ahmadtak-3212/flashlight_project/electrical/flashlight-full-v1-1/docs/Images/usbc.jpeg

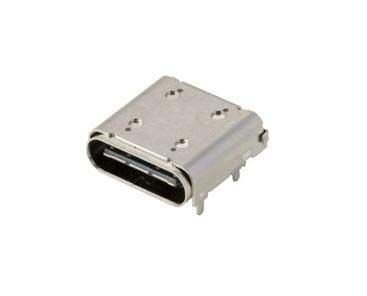
electrical/flashlight-full-v1-1/docs/Images/usbc.jpeg
