ahmadtak-3212/flashlight_project/firmware/flashlight-firmware-stm32/boards/platforms/ststm32/examples/mbed-rtos-custom-target/src/TARGET_STM32L452xE/TARGET_NUCLEO_L452RE_P/PeripheralPins.c

/* mbed Microcontroller Library
 *******************************************************************************
 * Copyright (c) 2019, STMicroelectronics
 * All rights reserved.
 *
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
 * Automatically generated from STM32L452RETxP.xml
 */

#include "PeripheralPins.h"
#include "mbed_toolchain.h"

//==============================================================================
// Notes
//
// - The pins mentioned Px_y_ALTz are alternative possibilities which use other
//   HW peripheral instances. You can use them the same way as any other "normal"
//   pin (i.e. PwmOut pwm(PA_7_ALT0);). These pins are not displayed on the board
//   pinout image on mbed.org.
//
// - The pins which are connected to other components present on the board have
//   the comment "Connected to xxx". The pin function may not work properly in this
//   case. These pins may not be displayed on the board pinout image on mbed.org.
//   Please read the board reference manual and schematic for more information.
//
// - Warning: pins connected to the default STDIO_UART_TX and STDIO_UART_RX pins are commented
//   See https://os.mbed.com/teams/ST/wiki/STDIO for more information.
//
//==============================================================================


//*** ADC ***

MBED_WEAK const PinMap PinMap_ADC[] = {
    {PA_0,       ADC_1, STM_PIN_DATA_EXT(STM_MODE_ANALOG, GPIO_NOPULL, 0, 5, 0)}, // ADC1_IN5
    {PA_1,       ADC_1, STM_PIN_DATA_EXT(STM_MODE_ANALOG, GPIO_NOPULL, 0, 6, 0)}, // ADC1_IN6
//  {PA_2,       ADC_1, STM_PIN_DATA_EXT(STM_MODE_ANALOG, GPIO_NOPULL, 0, 7, 0)}, // ADC1_IN7 // Connected to STDIO_UART_TX
//  {PA_3,       ADC_1, STM_PIN_DATA_EXT(STM_MODE_ANALOG, GPIO_NOPULL, 0, 8, 0)}, // ADC1_IN8 // Connected to STDIO_UART_RX
    {PA_4,       ADC_1, STM_PIN_DATA_EXT(STM_MODE_ANALOG, GPIO_NOPULL, 0, 9, 0)}, // ADC1_IN9 // Connected to SMPS_EN [ADP5301ACBZ_VEN]
    {PA_5,       ADC_1, STM_PIN_DATA_EXT(STM_MODE_ANALOG, GPIO_NOPULL, 0, 10, 0)}, // ADC1_IN10 // Connected to SMPS_V1
    {PA_6,       ADC_1, STM_PIN_DATA_EXT(STM_MODE_ANALOG, GPIO_NOPULL, 0, 11, 0)}, // ADC1_IN11 // Connected to SMPS_PG [ADP5301ACBZ_OUTOK]
    {PA_7,       ADC_1, STM_PIN_DATA_EXT(STM_MODE_ANALOG, GPIO_NOPULL, 0, 12, 0)}, // ADC1_IN12 // Connected to SMPS_SW [TS3A44159PWR_IN1_2]
    {PB_0,       ADC_1, STM_PIN_DATA_EXT(STM_MODE_ANALOG, GPIO_NOPULL, 0, 15, 0)}, // ADC1_IN15
    {PB_1,       ADC_1, STM_PIN_DATA_EXT(STM_MODE_ANALOG, GPIO_NOPULL, 0, 16, 0)}, // ADC1_IN16
    {PC_0,       ADC_1, STM_PIN_DATA_EXT(STM_MODE_ANALOG, GPIO_NOPULL, 0, 1, 0)}, // ADC1_IN1
    {PC_1,       ADC_1, STM_PIN_DATA_EXT(STM_MODE_ANALOG, GPIO_NOPULL, 0, 2, 0)}, // ADC1_IN2
    {PC_2,       ADC_1, STM_PIN_DATA_EXT(STM_MODE_ANALOG, GPIO_NOPULL, 0, 3, 0)}, // ADC1_IN3
    {PC_3,       ADC_1, STM_PIN_DATA_EXT(STM_MODE_ANALOG, GPIO_NOPULL, 0, 4, 0)}, // ADC1_IN4
    {PC_4,       ADC_1, STM_PIN_DATA_EXT(STM_MODE_ANALOG, GPIO_NOPULL, 0, 13, 0)}, // ADC1_IN13
    {NC, NC, 0}
};

// !!! SECTION TO BE CHECKED WITH DEVICE REFERENCE MANUAL
MBED_WEAK const PinMap PinMap_ADC_Internal[] = {
    {ADC_TEMP,   ADC_1,    STM_PIN_DATA_EXT(STM_MODE_ANALOG, GPIO_NOPULL, 0, 16, 0)},
    {ADC_VREF,   ADC_1,    STM_PIN_DATA_EXT(STM_MODE_ANALOG, GPIO_NOPULL, 0, 17, 0)},
    {ADC_VBAT,   ADC_1,    STM_PIN_DATA_EXT(STM_MODE_ANALOG, GPIO_NOPULL, 0, 18, 0)},
    {NC, NC, 0}
};

//*** DAC ***

MBED_WEAK const PinMap PinMap_DAC[] = {
    {PA_4,       DAC_1, STM_PIN_DATA_EXT(STM_MODE_ANALOG, GPIO_NOPULL, 0, 1, 0)}, // DAC1_OUT1 // Connected to SMPS_EN [ADP5301ACBZ_VEN]
    {NC, NC, 0}
};

//*** I2C ***

MBED_WEAK const PinMap PinMap_I2C_SDA[] = {
    {PA_10,      I2C_1, STM_PIN_DATA(STM_MODE_AF_OD, GPIO_NOPULL, GPIO_AF4_I2C1)},
    {PB_4,       I2C_3, STM_PIN_DATA(STM_MODE_AF_OD, GPIO_NOPULL, GPIO_AF4_I2C3)},
    {PB_7,       I2C_1, STM_PIN_DATA(STM_MODE_AF_OD, GPIO_NOPULL, GPIO_AF4_I2C1)},
    {PB_7_ALT0,  I2C_4, STM_PIN_DATA(STM_MODE_AF_OD, GPIO_NOPULL, GPIO_AF5_I2C4)},
    {PB_9,       I2C_1, STM_PIN_DATA(STM_MODE_AF_OD, GPIO_NOPULL, GPIO_AF4_I2C1)},
    {PB_11,      I2C_2, STM_PIN_DATA(STM_MODE_AF_OD, GPIO_NOPULL, GPIO_AF4_I2C2)},
    {PB_11_ALT0, I2C_4, STM_PIN_DATA(STM_MODE_AF_OD, GPIO_NOPULL, GPIO_AF3_I2C4)},
    {PB_14,      I2C_2, STM_PIN_DATA(STM_MODE_AF_OD, GPIO_NOPULL, GPIO_AF4_I2C2)},
    {PC_1,       I2C_3, STM_PIN_DATA(STM_MODE_AF_OD, GPIO_NOPULL, GPIO_AF4_I2C3)},
    {PC_1_ALT0,  I2C_4, STM_PIN_DATA(STM_MODE_AF_OD, GPIO_NOPULL, GPIO_AF2_I2C4)},
    {NC, NC, 0}
};

MBED_WEAK const PinMap PinMap_I2C_SCL[] = {
    {PA_7,       I2C_3, STM_PIN_DATA(STM_MODE_AF_OD, GPIO_NOPULL, GPIO_AF4_I2C3)}, // Connected to SMPS_SW [TS3A44159PWR_IN1_2]
    {PA_9,       I2C_1, STM_PIN_DATA(STM_MODE_AF_OD, GPIO_NOPULL, GPIO_AF4_I2C1)},
    {PB_6,       I2C_1, STM_PIN_DATA(STM_MODE_AF_OD, GPIO_NOPULL, GPIO_AF4_I2C1)},
    {PB_6_ALT0,  I2C_4, STM_PIN_DATA(STM_MODE_AF_OD, GPIO_NOPULL, GPIO_AF5_I2C4)},
    {PB_8,       I2C_1, STM_PIN_DATA(STM_MODE_AF_OD, GPIO_NOPULL, GPIO_AF4_I2C1)},
    {PB_10,      I2C_2, STM_PIN_DATA(STM_MODE_AF_OD, GPIO_NOPULL, GPIO_AF4_I2C2)},
    {PB_10_ALT0, I2C_4, STM_PIN_DATA(STM_MODE_AF_OD, GPIO_NOPULL, GPIO_AF3_I2C4)},
    {PB_13,      I2C_2, STM_PIN_DATA(STM_MODE_AF_OD, GPIO_NOPULL, GPIO_AF4_I2C2)}, // Connected to LD4 [green Led]
    {PC_0,       I2C_3, STM_PIN_DATA(STM_MODE_AF_OD, GPIO_NOPULL, GPIO_AF4_I2C3)},
    {PC_0_ALT0,  I2C_4, STM_PIN_DATA(STM_MODE_AF_OD, GPIO_NOPULL, GPIO_AF2_I2C4)},
    {NC, NC, 0}
};

//*** PWM ***

// TIM2 cannot be used because already used by the us_ticker
// You have to comment all PWM using TIM_MST defined in hal_tick.h file
//  or update python script (check TIM_MST_LIST) and re-run it
MBED_WEAK const PinMap PinMap_PWM[] = {
//  {PA_0,       PWM_2,  STM_PIN_DATA_EXT(STM_MODE_AF_PP, GPIO_NOPULL, GPIO_AF1_TIM2, 1, 0)}, // TIM2_CH1 // TIM2 used by us_ticker
//  {PA_1,       PWM_2,  STM_PIN_DATA_EXT(STM_MODE_AF_PP, GPIO_NOPULL, GPIO_AF1_TIM2, 2, 0)}, // TIM2_CH2 // TIM2 used by us_ticker
    {PA_1,       PWM_15, STM_PIN_DATA_EXT(STM_MODE_AF_PP, GPIO_NOPULL, GPIO_AF14_TIM15, 1, 1)}, // TIM15_CH1N
//  {PA_2,       PWM_2,  STM_PIN_DATA_EXT(STM_MODE_AF_PP, GPIO_NOPULL, GPIO_AF1_TIM2, 3, 0)}, // TIM2_CH3 // Connected to STDIO_UART_TX
//  {PA_2,       PWM_15, STM_PIN_DATA_EXT(STM_MODE_AF_PP, GPIO_NOPULL, GPIO_AF14_TIM15, 1, 0)}, // TIM15_CH1 // Connected to STDIO_UART_TX
//  {PA_3,       PWM_2,  STM_PIN_DATA_EXT(STM_MODE_AF_PP, GPIO_NOPULL, GPIO_AF1_TIM2, 4, 0)}, // TIM2_CH4 // Connected to STDIO_UART_RX
//  {PA_3,       PWM_15, STM_PIN_DATA_EXT(STM_MODE_AF_PP, GPIO_NOPULL, GPIO_AF14_TIM15, 2, 0)}, // TIM15_CH2 // Connected to STDIO_UART_RX
//  {PA_5,       PWM_2,  STM_PIN_DATA_EXT(STM_MODE_AF_PP, GPIO_NOPULL, GPIO_AF1_TIM2, 1, 0)}, // TIM2_CH1 // Connected to SMPS_V1, TIM2 used by us_ticker
    {PA_6,       PWM_3,  STM_PIN_DATA_EXT(STM_MODE_AF_PP, GPIO_NOPULL, GPIO_AF2_TIM3, 1, 0)}, // TIM3_CH1 // Connected to SMPS_PG [ADP5301ACBZ_OUTOK]
    {PA_6_ALT0,  PWM_16, STM_PIN_DATA_EXT(STM_MODE_AF_PP, GPIO_NOPULL, GPIO_AF14_TIM16, 1, 0)}, // TIM16_CH1 // Connected to SMPS_PG [ADP5301ACBZ_OUTOK]
    {PA_7,       PWM_1,  STM_PIN_DATA_EXT(STM_MODE_AF_PP, GPIO_NOPULL, GPIO_AF1_TIM1, 1, 1)}, // TIM1_CH1N // Connected to SMPS_SW [TS3A44159PWR_IN1_2]
    {PA_7_ALT0,  PWM_3,  STM_PIN_DATA_EXT(STM_MODE_AF_PP, GPIO_NOPULL, GPIO_AF2_TIM3, 2, 0)}, // TIM3_CH2 // Connected to SMPS_SW [TS3A44159PWR_IN1_2]
    {PA_8,       PWM_1,  STM_PIN_DATA_EXT(STM_MODE_AF_PP, GPIO_NOPULL, GPIO_AF1_TIM1, 1, 0)}, // TIM1_CH1
    {PA_9,       PWM_1,  STM_PIN_DATA_EXT(STM_MODE_AF_PP, GPIO_NOPULL, GPIO_AF1_TIM1, 2, 0)}, // TIM1_CH2
    {PA_10,      PWM_1,  STM_PIN_DATA_EXT(STM_MODE_AF_PP, GPIO_NOPULL, GPIO_AF1_TIM1, 3, 0)}, // TIM1_CH3
    {PA_11,      PWM_1,  STM_PIN_DATA_EXT(STM_MODE_AF_PP, GPIO_NOPULL, GPIO_AF1_TIM1, 4, 0)}, // TIM1_CH4
//  {PA_15,      PWM_2,  STM_PIN_DATA_EXT(STM_MODE_AF_PP, GPIO_NOPULL, GPIO_AF1_TIM2, 1, 0)}, // TIM2_CH1 // TIM2 used by us_ticker
    {PB_0,       PWM_1,  STM_PIN_DATA_EXT(STM_MODE_AF_PP, GPIO_NOPULL, GPIO_AF1_TIM1, 2, 1)}, // TIM1_CH2N
    {PB_0_ALT0,  PWM_3,  STM_PIN_DATA_EXT(STM_MODE_AF_PP, GPIO_NOPULL, GPIO_AF2_TIM3, 3, 0)}, // TIM3_CH3
    {PB_1,       PWM_1,  STM_PIN_DATA_EXT(STM_MODE_AF_PP, GPIO_NOPULL, GPIO_AF1_TIM1, 3, 1)}, // TIM1_CH3N
    {PB_1_ALT0,  PWM_3,  STM_PIN_DATA_EXT(STM_MODE_AF_PP, GPIO_NOPULL, GPIO_AF2_TIM3, 4, 0)}, // TIM3_CH4
//  {PB_3,       PWM_2,  STM_PIN_DATA_EXT(STM_MODE_AF_PP, GPIO_NOPULL, GPIO_AF1_TIM2, 2, 0)}, // TIM2_CH2 // TIM2 used by us_ticker
    {PB_4,       PWM_3,  STM_PIN_DATA_EXT(STM_MODE_AF_PP, GPIO_NOPULL, GPIO_AF2_TIM3, 1, 0)}, // TIM3_CH1
    {PB_5,       PWM_3,  STM_PIN_DATA_EXT(STM_MODE_AF_PP, GPIO_NOPULL, GPIO_AF2_TIM3, 2, 0)}, // TIM3_CH2
    {PB_6,       PWM_16, STM_PIN_DATA_EXT(STM_MODE_AF_PP, GPIO_NOPULL, GPIO_AF14_TIM16, 1, 1)}, // TIM16_CH1N
    {PB_8,       PWM_16, STM_PIN_DATA_EXT(STM_MODE_AF_PP, GPIO_NOPULL, GPIO_AF14_TIM16, 1, 0)}, // TIM16_CH1
//  {PB_10,      PWM_2,  STM_PIN_DATA_EXT(STM_MODE_AF_PP, GPIO_NOPULL, GPIO_AF1_TIM2, 3, 0)}, // TIM2_CH3 // TIM2 used by usticker
//  {PB_11,      PWM_2,  STM_PIN_DATA_EXT(STM_MODE_AF_PP, GPIO_NOPULL, GPIO_AF1_TIM2, 4, 0)}, // TIM2_CH4 // TIM2 used by usticker
    {PB_13,      PWM_1,  STM_PIN_DATA_EXT(STM_MODE_AF_PP, GPIO_NOPULL, GPIO_AF1_TIM1, 1, 1)}, // TIM1_CH1N // Connected to LD4 [green Led]
    {PB_13_ALT0, PWM_15, STM_PIN_DATA_EXT(STM_MODE_AF_PP, GPIO_NOPULL, GPIO_AF14_TIM15, 1, 1)}, // TIM15_CH1N // Connected to LD4 [green Led]
    {PB_14,      PWM_1,  STM_PIN_DATA_EXT(STM_MODE_AF_PP, GPIO_NOPULL, GPIO_AF1_TIM1, 2, 1)}, // TIM1_CH2N
    {PB_14_ALT0, PWM_15, STM_PIN_DATA_EXT(STM_MODE_AF_PP, GPIO_NOPULL, GPIO_AF14_TIM15, 1, 0)}, // TIM15_CH1
    {PB_15,      PWM_1,  STM_PIN_DATA_EXT(STM_MODE_AF_PP, GPIO_NOPULL, GPIO_AF1_TIM1, 3, 1)}, // TIM1_CH3N
    {PB_15_ALT0, PWM_15, STM_PIN_DATA_EXT(STM_MODE_AF_PP, GPIO_NOPULL, GPIO_AF14_TIM15, 2, 0)}, // TIM15_CH2
    {PC_6,       PWM_3,  STM_PIN_DATA_EXT(STM_MODE_AF_PP, GPIO_NOPULL, GPIO_AF2_TIM3, 1, 0)}, // TIM3_CH1
    {PC_7,       PWM_3,  STM_PIN_DATA_EXT(STM_MODE_AF_PP, GPIO_NOPULL, GPIO_AF2_TIM3, 2, 0)}, // TIM3_CH2
    {PC_8,       PWM_3,  STM_PIN_DATA_EXT(STM_MODE_AF_PP, GPIO_NOPULL, GPIO_AF2_TIM3, 3, 0)}, // TIM3_CH3
    {PC_9,       PWM_3,  STM_PIN_DATA_EXT(STM_MODE_AF_PP, GPIO_NOPULL, GPIO_AF2_TIM3, 4, 0)}, // TIM3_CH4
    {NC, NC, 0}
};

//*** SERIAL ***

MBED_WEAK const PinMap PinMap_UART_TX[] = {
    {PA_0,       UART_4,  STM_PIN_DATA(STM_MODE_AF_PP, GPIO_PULLUP, GPIO_AF8_UART4)},
    {PA_2,       UART_2,  STM_PIN_DATA(STM_MODE_AF_PP, GPIO_PULLUP, GPIO_AF7_USART2)}, // Connected to STDIO_UART_TX
    {PA_2_ALT0,  LPUART_1, STM_PIN_DATA(STM_MODE_AF_PP, GPIO_PULLUP, GPIO_AF8_LPUART1)}, // Connected to STDIO_UART_TX
    {PA_9,       UART_1,  STM_PIN_DATA(STM_MODE_AF_PP, GPIO_PULLUP, GPIO_AF7_USART1)},
    {PB_6,       UART_1,  STM_PIN_DATA(STM_MODE_AF_PP, GPIO_PULLUP, GPIO_AF7_USART1)},
    {PB_10,      UART_3,  STM_PIN_DATA(STM_MODE_AF_PP, GPIO_PULLUP, GPIO_AF7_USART3)},
    {PB_11,      LPUART_1, STM_PIN_DATA(STM_MODE_AF_PP, GPIO_PULLUP, GPIO_AF8_LPUART1)},
    {PC_1,       LPUART_1, STM_PIN_DATA(STM_MODE_AF_PP, GPIO_PULLUP, GPIO_AF8_LPUART1)},
    {PC_4,       UART_3,  STM_PIN_DATA(STM_MODE_AF_PP, GPIO_PULLUP, GPIO_AF7_USART3)},
    {PC_10,      UART_3,  STM_PIN_DATA(STM_MODE_AF_PP, GPIO_PULLUP, GPIO_AF7_USART3)},
    {PC_10_ALT0, UART_4,  STM_PIN_DATA(STM_MODE_AF_PP, GPIO_PULLUP, GPIO_AF8_UART4)},
    {NC, NC, 0}
};

MBED_WEAK const PinMap PinMap_UART_RX[] = {
    {PA_1,       UART_4,  STM_PIN_DATA(STM_MODE_AF_PP, GPIO_PULLUP, GPIO_AF8_UART4)},
    {PA_3,       UART_2,  STM_PIN_DATA(STM_MODE_AF_PP, GPIO_PULLUP, GPIO_AF7_USART2)}, // Connected to STDIO_UART_RX
    {PA_3_ALT0,  LPUART_1, STM_PIN_DATA(STM_MODE_AF_PP, GPIO_PULLUP, GPIO_AF8_LPUART1)}, // Connected to STDIO_UART_RX
    {PA_10,      UART_1,  STM_PIN_DATA(STM_MODE_AF_PP, GPIO_PULLUP, GPIO_AF7_USART1)},
    {PA_15,      UART_2,  STM_PIN_DATA(STM_MODE_AF_PP, GPIO_PULLUP, GPIO_AF3_USART2)},
    {PB_7,       UART_1,  STM_PIN_DATA(STM_MODE_AF_PP, GPIO_PULLUP, GPIO_AF7_USART1)},
    {PB_10,      LPUART_1, STM_PIN_DATA(STM_MODE_AF_PP, GPIO_PULLUP, GPIO_AF8_LPUART1)},
    {PB_11,      UART_3,  STM_PIN_DATA(STM_MODE_AF_PP, GPIO_PULLUP, GPIO_AF7_USART3)},
    {PC_0,       LPUART_1, STM_PIN_DATA(STM_MODE_AF_PP, GPIO_PULLUP, GPIO_AF8_LPUART1)},
    {PC_11,      UART_3,  STM_PIN_DATA(STM_MODE_AF_PP, GPIO_PULLUP, GPIO_AF7_USART3)},
    {PC_11_ALT0, UART_4,  STM_PIN_DATA(STM_MODE_AF_PP, GPIO_PULLUP, GPIO_AF8_UART4)},
    {NC, NC, 0}
};

MBED_WEAK const PinMap PinMap_UART_RTS[] = {
    {PA_1,       UART_2,  STM_PIN_DATA(STM_MODE_AF_PP, GPIO_PULLUP, GPIO_AF7_USART2)},
    {PA_12,      UART_1,  STM_PIN_DATA(STM_MODE_AF_PP, GPIO_PULLUP, GPIO_AF7_USART1)},
    {PA_15,      UART_3,  STM_PIN_DATA(STM_MODE_AF_PP, GPIO_PULLUP, GPIO_AF7_USART3)},
    {PA_15_ALT0, UART_4,  STM_PIN_DATA(STM_MODE_AF_PP, GPIO_PULLUP, GPIO_AF8_UART4)},
    {PB_1,       UART_3,  STM_PIN_DATA(STM_MODE_AF_PP, GPIO_PULLUP, GPIO_AF7_USART3)},
    {PB_1_ALT0,  LPUART_1, STM_PIN_DATA(STM_MODE_AF_PP, GPIO_PULLUP, GPIO_AF8_LPUART1)},
    {PB_3,       UART_1,  STM_PIN_DATA(STM_MODE_AF_PP, GPIO_PULLUP, GPIO_AF7_USART1)},
    {PB_12,      LPUART_1, STM_PIN_DATA(STM_MODE_AF_PP, GPIO_PULLUP, GPIO_AF8_LPUART1)},
    {PB_14,      UART_3,  STM_PIN_DATA(STM_MODE_AF_PP, GPIO_PULLUP, GPIO_AF7_USART3)},
    {NC, NC, 0}
};

MBED_WEAK const PinMap PinMap_UART_CTS[] = {
    {PA_0,       UART_2,  STM_PIN_DATA(STM_MODE_AF_PP, GPIO_PULLUP, GPIO_AF7_USART2)},
    {PA_6,       UART_3,  STM_PIN_DATA(STM_MODE_AF_PP, GPIO_PULLUP, GPIO_AF7_USART3)}, // Connected to SMPS_PG [ADP5301ACBZ_OUTOK]
    {PA_6_ALT0,  LPUART_1, STM_PIN_DATA(STM_MODE_AF_PP, GPIO_PULLUP, GPIO_AF8_LPUART1)}, // Connected to SMPS_PG [ADP5301ACBZ_OUTOK]
    {PA_11,      UART_1,  STM_PIN_DATA(STM_MODE_AF_PP, GPIO_PULLUP, GPIO_AF7_USART1)},
    {PB_4,       UART_1,  STM_PIN_DATA(STM_MODE_AF_PP, GPIO_PULLUP, GPIO_AF7_USART1)},
    {PB_7,       UART_4,  STM_PIN_DATA(STM_MODE_AF_PP, GPIO_PULLUP, GPIO_AF8_UART4)},
    {PB_13,      UART_3,  STM_PIN_DATA(STM_MODE_AF_PP, GPIO_PULLUP, GPIO_AF7_USART3)}, // Connected to LD4 [green Led]
    {PB_13_ALT0, LPUART_1, STM_PIN_DATA(STM_MODE_AF_PP, GPIO_PULLUP, GPIO_AF8_LPUART1)}, // Connected to LD4 [green Led]
    {NC, NC, 0}
};

//*** SPI ***

MBED_WEAK const PinMap PinMap_SPI_MOSI[] = {
    {PA_7,       SPI_1, STM_PIN_DATA(STM_MODE_AF_PP, GPIO_NOPULL, GPIO_AF5_SPI1)}, // Connected to SMPS_SW [TS3A44159PWR_IN1_2]
    {PA_12,      SPI_1, STM_PIN_DATA(STM_MODE_AF_PP, GPIO_NOPULL, GPIO_AF5_SPI1)},
    {PB_5,       SPI_1, STM_PIN_DATA(STM_MODE_AF_PP, GPIO_NOPULL, GPIO_AF5_SPI1)},
    {PB_5_ALT0,  SPI_3, STM_PIN_DATA(STM_MODE_AF_PP, GPIO_NOPULL, GPIO_AF6_SPI3)},
    {PB_15,      SPI_2, STM_PIN_DATA(STM_MODE_AF_PP, GPIO_NOPULL, GPIO_AF5_SPI2)},
    {PC_3,       SPI_2, STM_PIN_DATA(STM_MODE_AF_PP, GPIO_NOPULL, GPIO_AF5_SPI2)},
    {PC_12,      SPI_3, STM_PIN_DATA(STM_MODE_AF_PP, GPIO_NOPULL, GPIO_AF6_SPI3)},
    {NC, NC, 0}
};

MBED_WEAK const PinMap PinMap_SPI_MISO[] = {
    {PA_6,       SPI_1, STM_PIN_DATA(STM_MODE_AF_PP, GPIO_NOPULL, GPIO_AF5_SPI1)}, // Connected to SMPS_PG [ADP5301ACBZ_OUTOK]
    {PA_11,      SPI_1, STM_PIN_DATA(STM_MODE_AF_PP, GPIO_NOPULL, GPIO_AF5_SPI1)},
    {PB_4,       SPI_1, STM_PIN_DATA(STM_MODE_AF_PP, GPIO_NOPULL, GPIO_AF5_SPI1)},
    {PB_4_ALT0,  SPI_3, STM_PIN_DATA(STM_MODE_AF_PP, GPIO_NOPULL, GPIO_AF6_SPI3)},
    {PB_14,      SPI_2, STM_PIN_DATA(STM_MODE_AF_PP, GPIO_NOPULL, GPIO_AF5_SPI2)},
    {PC_2,       SPI_2, STM_PIN_DATA(STM_MODE_AF_PP, GPIO_NOPULL, GPIO_AF5_SPI2)},
    {PC_11,      SPI_3, STM_PIN_DATA(STM_MODE_AF_PP, GPIO_NOPULL, GPIO_AF6_SPI3)},
    {NC, NC, 0}
};

MBED_WEAK const PinMap PinMap_SPI_SCLK[] = {
    {PA_1,       SPI_1, STM_PIN_DATA(STM_MODE_AF_PP, GPIO_NOPULL, GPIO_AF5_SPI1)},
    {PA_5,       SPI_1, STM_PIN_DATA(STM_MODE_AF_PP, GPIO_NOPULL, GPIO_AF5_SPI1)}, // Connected to SMPS_V1
    {PB_3,       SPI_1, STM_PIN_DATA(STM_MODE_AF_PP, GPIO_NOPULL, GPIO_AF5_SPI1)},
    {PB_3_ALT0,  SPI_3, STM_PIN_DATA(STM_MODE_AF_PP, GPIO_NOPULL, GPIO_AF6_SPI3)},
    {PB_10,      SPI_2, STM_PIN_DATA(STM_MODE_AF_PP, GPIO_NOPULL, GPIO_AF5_SPI2)},
    {PB_13,      SPI_2, STM_PIN_DATA(STM_MODE_AF_PP, GPIO_NOPULL, GPIO_AF5_SPI2)}, // Connected to LD4 [green Led]
    {PC_10,      SPI_3, STM_PIN_DATA(STM_MODE_AF_PP, GPIO_NOPULL, GPIO_AF6_SPI3)},
    {NC, NC, 0}
};

MBED_WEAK const PinMap PinMap_SPI_SSEL[] = {
    {PA_4,       SPI_1, STM_PIN_DATA(STM_MODE_AF_PP, GPIO_NOPULL, GPIO_AF5_SPI1)}, // Connected to SMPS_EN [ADP5301ACBZ_VEN]
    {PA_4_ALT0,  SPI_3, STM_PIN_DATA(STM_MODE_AF_PP, GPIO_NOPULL, GPIO_AF6_SPI3)}, // Connected to SMPS_EN [ADP5301ACBZ_VEN]
    {PA_15,      SPI_1, STM_PIN_DATA(STM_MODE_AF_PP, GPIO_NOPULL, GPIO_AF5_SPI1)},
    {PA_15_ALT0, SPI_3, STM_PIN_DATA(STM_MODE_AF_PP, GPIO_NOPULL, GPIO_AF6_SPI3)},
    {PB_0,       SPI_1, STM_PIN_DATA(STM_MODE_AF_PP, GPIO_NOPULL, GPIO_AF5_SPI1)},
    {PB_9,       SPI_2, STM_PIN_DATA(STM_MODE_AF_PP, GPIO_NOPULL, GPIO_AF5_SPI2)},
    {PB_12,      SPI_2, STM_PIN_DATA(STM_MODE_AF_PP, GPIO_NOPULL, GPIO_AF5_SPI2)},
    {NC, NC, 0}
};

//*** CAN ***

MBED_WEAK const PinMap PinMap_CAN_RD[] = {
    {PA_11,      CAN_1, STM_PIN_DATA(STM_MODE_AF_PP, GPIO_NOPULL, GPIO_AF9_CAN1)},
    {PB_5,       CAN_1, STM_PIN_DATA(STM_MODE_AF_PP, GPIO_NOPULL, GPIO_AF3_CAN1)},
    {PB_8,       CAN_1, STM_PIN_DATA(STM_MODE_AF_PP, GPIO_NOPULL, GPIO_AF9_CAN1)},
    {PB_12,      CAN_1, STM_PIN_DATA(STM_MODE_AF_PP, GPIO_NOPULL, GPIO_AF10_CAN1)},
    {NC, NC, 0}
};

MBED_WEAK const PinMap PinMap_CAN_TD[] = {
    {PA_12,      CAN_1, STM_PIN_DATA(STM_MODE_AF_PP, GPIO_NOPULL, GPIO_AF9_CAN1)},
    {PB_6,       CAN_1, STM_PIN_DATA(STM_MODE_AF_PP, GPIO_NOPULL, GPIO_AF8_CAN1)},
    {PB_9,       CAN_1, STM_PIN_DATA(STM_MODE_AF_PP, GPIO_NOPULL, GPIO_AF9_CAN1)},
    {PB_13,      CAN_1, STM_PIN_DATA(STM_MODE_AF_PP, GPIO_NOPULL, GPIO_AF10_CAN1)}, // Connected to LD4 [green Led]
    {NC, NC, 0}
};

//*** QUADSPI ***

MBED_WEAK const PinMap PinMap_QSPI_DATA0[] = {
    {PB_1,      QSPI_1, STM_PIN_DATA(STM_MODE_AF_PP, GPIO_PULLUP, GPIO_AF10_QUADSPI)},  // QUADSPI_BK1_IO0
    {NC, NC, 0}
};

MBED_WEAK const PinMap PinMap_QSPI_DATA1[] = {
    {PB_0,      QSPI_1, STM_PIN_DATA(STM_MODE_AF_PP, GPIO_PULLUP, GPIO_AF10_QUADSPI)},  // QUADSPI_BK1_IO1
    {NC, NC, 0}
};

MBED_WEAK const PinMap PinMap_QSPI_DATA2[] = {
    {PA_7,      QSPI_1, STM_PIN_DATA(STM_MODE_AF_PP, GPIO_PULLUP, GPIO_AF10_QUADSPI)},  // QUADSPI_BK1_IO2 // Connected to SMPS_SW [TS3A44159PWR_IN1_2]
    {NC, NC, 0}
};

MBED_WEAK const PinMap PinMap_QSPI_DATA3[] = {
    {PA_6,      QSPI_1, STM_PIN_DATA(STM_MODE_AF_PP, GPIO_PULLUP, GPIO_AF10_QUADSPI)},  // QUADSPI_BK1_IO3 // Connected to SMPS_PG [ADP5301ACBZ_OUTOK]
    {NC, NC, 0}
};

MBED_WEAK const PinMap PinMap_QSPI_SCLK[] = {
//  {PA_3,      QSPI_1, STM_PIN_DATA(STM_MODE_AF_PP, GPIO_PULLUP, GPIO_AF10_QUADSPI)},  // QUADSPI_CLK // Connected to STDIO_UART_RX
    {PB_10,     QSPI_1, STM_PIN_DATA(STM_MODE_AF_PP, GPIO_PULLUP, GPIO_AF10_QUADSPI)},  // QUADSPI_CLK
    {NC, NC, 0}
};

MBED_WEAK const PinMap PinMap_QSPI_SSEL[] = {
//  {PA_2,      QSPI_1, STM_PIN_DATA(STM_MODE_AF_PP, GPIO_PULLUP, GPIO_AF10_QUADSPI)},  // QUADSPI_BK1_NCS // Connected to STDIO_UART_TX
    {PB_11,     QSPI_1, STM_PIN_DATA(STM_MODE_AF_PP, GPIO_PULLUP, GPIO_AF10_QUADSPI)},  // QUADSPI_BK1_NCS
    {NC, NC, 0}
};

//*** USBDEVICE ***

MBED_WEAK const PinMap PinMap_USB_FS[] = {
    {PA_11,     USB_FS, STM_PIN_DATA(STM_MODE_INPUT, GPIO_NOPULL, GPIO_AF10_USB_FS)}, // USB_DM
    {PA_12,     USB_FS, STM_PIN_DATA(STM_MODE_INPUT, GPIO_NOPULL, GPIO_AF10_USB_FS)}, // USB_DP
//  {PA_13,     USB_FS, STM_PIN_DATA(STM_MODE_AF_PP, GPIO_PULLUP, GPIO_AF10_USB_FS)}, // USB_NOE
//  {PC_9,      USB_FS, STM_PIN_DATA(STM_MODE_AF_PP, GPIO_PULLUP, GPIO_AF10_USB_FS)}, // USB_NOE
    {NC, NC, 0}
};
